MOSH-Insa-Toulouse/5ISS_Heusse_Holmes_GasSensor/LTSpice/Ampli.asc

C1: cap; 100n
C2: cap; 100n
C3: cap; 100n
C4: cap; 1µ
C5: cap; 1p
R1: res; 100k
R2: res; 1k
R3: res; 100k
R4: res; 1k
R5: res; 10k
U1: LTC1050
V1: voltage; 5
V2: voltage; SINE(0 325 50)
V3: voltage; PULSE(0 1 0.2 0.1 0.1 20)
X1: capteur
Named nets: 0, Vcc, ADC
.tran 0 2 0 10m
;op
;ac dec 100 0.01 100Meg
.param G0=10n
.param G1=10n
